Smashcat/circular-display-prototyping-board/Arduino/GC9A01/examples/SpriteScale/data.h

// The following sprite data has been generated using the genSprite.php script. 

// Character set
const uint8_t gData0[760]={B00000000,B00000000,B00000000,B00000000,B00000000,B00000000,B00000000,B00000000,B00000110,B00001111,B00001111,B00000110,B00000110,B00000000,B00000110,B00000000,B00011011,B00010010,B00001001,B00000000,B00000000,B00000000,B00000000,B00000000,B00110110,B00110110,B01111111,B00110110,B01111111,B00110110,B00110110,B00000000,B00001000,B00111110,B00001011,B00111110,B01101000,B00111111,B00001000,B00000000,B00000000,B01100110,B00110101,B00011011,B01101100,B01010110,B00110011,B00000000,B00011100,B00110010,B00011100,B00011110,B01110011,B00110011,B01011110,B00000000,B00000011,B00000010,B00000001,B00000000,B00000000,B00000000,B00000000,B00000000,B00001100,B00000110,B00000011,B00000011,B00000011,B00000110,B00001100,B00000000,B00000011,B00000110,B00001100,B00001100,B00001100,B00000110,B00000011,B00000000,B00000000,B01100110,B00111100,B11111111,B00111100,B01100110,B00000000,B00000000,B00000000,B00001100,B00001100,B00111111,B00001100,B00001100,B00000000,B00000000,B00000000,B00000000,B00000000,B00000000,B00000000,B00000011,B00000010,B00000001,B00000000,B00000000,B00000000,B01111111,B00000000,B00000000,B00000000,B00000000,B00000000,B00000000,B00000000,B00000000,B00000000,B00000000,B00000011,B00000000,B01000000,B01100000,B00110000,B00011000,B00001100,B00000110,B00000011,B00000000,B00111110,B01110011,B01111011,B01101111,B01100111,B01100111,B00111110,B00000000,B00011000,B00011100,B00011110,B00011000,B00011000,B00011000,B01111110,B00000000,B00111110,B01100011,B01100000,B00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
const uint8_t charWidth[95]={4,4,5,7,7,7,7,2,4,4,8,6,2,7,2,7,7,7,7,7,7,7,7,7,7,7,2,2,5,6,5,6,7,7,7,7,7,7,7,7,7,4,7,7,7,7,7,7,7,7,7,7,6,7,7,7,7,7,7,4,7,4,7,8,2,7,7,7,7,7,6,7,7,4,6,7,6,7,7,7,7,7,7,7,6,7,7,7,7,6,6,5,2,5,7};

// Big ghost
const uint8_t gData4[2920]={B00000000,B00000000,B00000000,B00000000,B00000000,B00000000,B00000000,B01010100,B01010101,B01010101,B01010101,B01010101,B00010101,B00000000,B00000000,B00000000,B00000000,B00000000,B00000000,B00000000,B00000000,B00000000,B00000000,B00000000,B00000000,B00000000,B00000000,B10100100,B10101010,B10101010,B10101010,B10101010,B00011010,B00000000,B00000000,B00000000,B00000000,B00000000,B00000000,B00000000,B00000000,B00000000,B00000000,B00000000,B00000000,B00000000,B00000000,B10100100,B10101010,B10101010,B10101010,B10101010,B00011010,B00000000,B00000000,B00000000,B00000000,B00000000,B00000000,B00000000,B00000000,B00000000,B00000000,B00000000,B00000000,B00000000,B00000000,B10100100,B10101010,B10101010,B10101010,B10101010,B00011010,B00000000,B00000000,B00000000,B00000000,B00000000,B00000000,B00000000,B00000000,B00000000,B00000000,B00000000,B00000000,B00000000,B00000000,B10100100,B10101010,B10101010,B10101010,B10101010,B00011010,B00000000,B00000000,B00000000,B00000000,B00000000,B00000000,B00000000,B00000000,B00000000,B00000000,B00000000,B01000000,B01010101,B01010101,B10100101,B10101010,B10101010,B10101010,B10101010,B01011010,B01010101,B01010101,B00000001,B00000000,B00000000,B00000000,B00000000,B00000000,B00000000,B00000000,B00000000,B01000000,B10101010,B10101010,B10101010,B10101010,B10101010,B10101010,B10101010,B10101010,B10101010,B10101010,B00000001,B00000000,B00000000,B00000000,B00000000,B00000000,B00000000,B00000000,B00000000,B01000000,B10101010,B10101010,B1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
  {{0,1,2, 5,5,5, 8,8,8, 11,11,11, 14,14,14},{0,1,2, 3,5,5, 6,7,8, 9,11,11,  12,13,14}},  // 7 -> 8
  {{0,1,2, 3,5,5, 6,7,8, 9,11,11,  12,13,14},{0,1,2, 3,5,5, 6,7,8, 12,11,11, 12,13,14}},  // 8 -> 9
};
