Smashcat/circular-display-prototyping-board/docs/IMG_2488.jpg

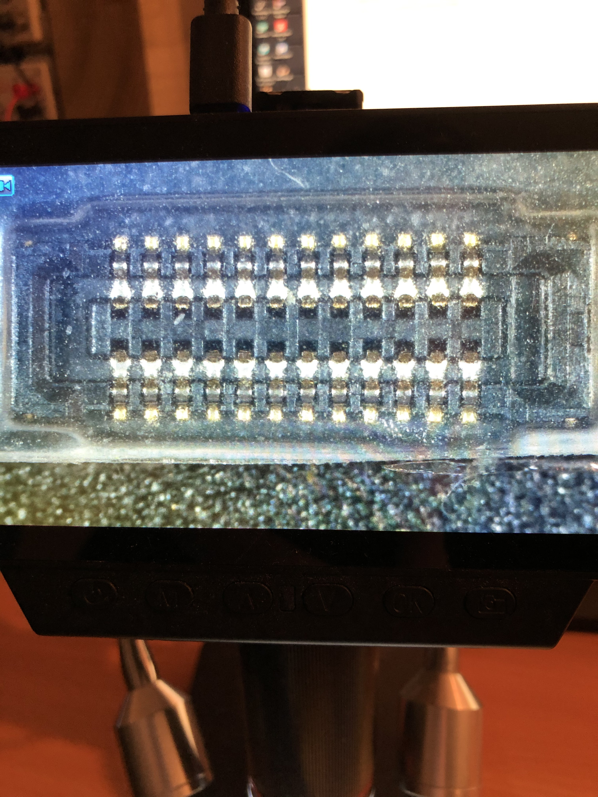
docs/IMG_2488.jpg
