Smashcat/circular-display-prototyping-board/docs/IMG_2489.jpg

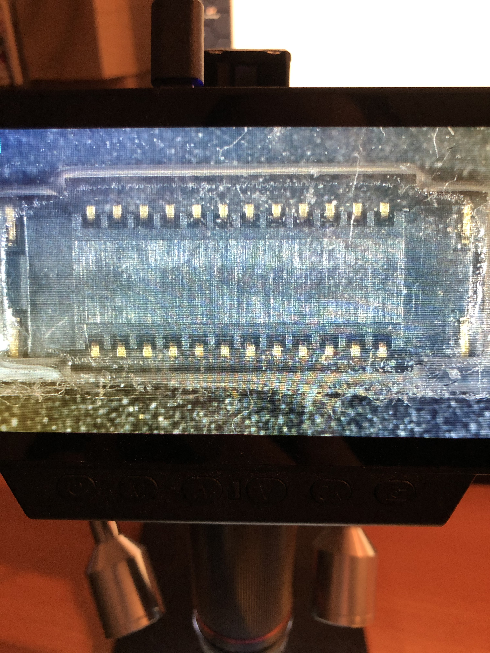
docs/IMG_2489.jpg
